SociableThings/soth-core/avr/SothCoreATXMEGA32E5/SothCore/MotionControl.h

/*
 * MotionControl.h
 *
 * Author: Hideyuki Takei <hide@soth.io>
 */ 


#ifndef MOTIONCONTROL_H_
#define MOTIONCONTROL_H_


void setStandaloneMotion();
void setOldStandaloneMotion();


#endif /* MOTIONCONTROL_H_ */
