SociableThings/soth-core/avr/SothCoreATXMEGA32E5/SothCore/UsartCommunication.h

/*
 * UsartCommunication.h
 *
 *  Author: Hideyuki Takei <hide@soth.io>
 */ 


#ifndef USART_COMMUNICATION_H_
#define USART_COMMUNICATION_H_


void initUsartComm();
void sendCharacterToComm(const char);
void sendStringToComm(const char *);
uint16_t recvCharacters(char* buf, uint16_t length);


#endif /* USART_COMMUNICATION_H_ */
